takumasendeke/hygiene-hero/firmware/src/Bitmaps.cpp

#include "Bitmaps.h"

// ICON 1: Wet Hands
static const unsigned char icon[ICON_FRAMES][ICON_BYTES] PROGMEM = {
  0x00, 0x00, 0x00, 0x00, 0x00, 0x00, 0x00, 0x00, 0x00, 0x00, 0x00, 0x00,
   0x00, 0x00, 0x00, 0x00, 0x00, 0x00, 0x00, 0x00, 0x00, 0x00, 0x00, 0x00,
   0x00, 0x00, 0x00, 0x00, 0x00, 0x00, 0x00, 0x00, 0x00, 0x00, 0x00, 0x00,
   0x00, 0x00, 0x00, 0x00, 0x00, 0x00, 0x00, 0xfe, 0xff, 0xff, 0x1f, 0x00,
   0x00, 0x00, 0x00, 0x00, 0x00, 0x00, 0x00, 0x00, 0x00, 0x00, 0x00, 0xff,
   0xff, 0xff, 0xff, 0x00, 0x38, 0x8e, 0xf3, 0xef, 0x7f, 0x00, 0x00, 0x00,
   0x00, 0x00, 0x00, 0xff, 0xff, 0xff, 0xff, 0x03, 0x38, 0x8e, 0x73, 0x00,
   0x0e, 0x00, 0x00, 0x00, 0x00, 0x00, 0x00, 0x0f, 0x00, 0x00, 0xfc, 0x0f,
   0x38, 0x9f, 0x73, 0x00, 0x0e, 0x00, 0x00, 0x00, 0x00, 0x00, 0x00, 0x07,
   0x00, 0x00, 0xe0, 0x1f, 0x38, 0x9f, 0x73, 0x00, 0x0e, 0x00, 0x00, 0x00,
   0x00, 0x00, 0x00, 0x07, 0x00, 0x00, 0x80, 0x7f, 0x30, 0x9f, 0x71, 0x00,
   0x0e, 0x00, 0x00, 0x00, 0x00, 0x00, 0x00, 0x07, 0x00, 0x00, 0x00, 0xfe,
   0x70, 0xdb, 0xf1, 0x0f, 0x0e, 0x00, 0x00, 0x00, 0x00, 0x00, 0x00, 0x07,
   0x00, 0x00, 0x00, 0xfc, 0xf0, 0xfb, 0x71, 0x00, 0x0e, 0x00, 0x00, 0x00,
   0x00, 0x00, 0x00, 0x0f, 0x00, 0x00, 0x00, 0xf0, 0xf0, 0xf9, 0x70, 0x00,
   0x0e, 0x00, 0x00, 0x00, 0x00, 0x00, 0x00, 0x3f, 0x00, 0x00, 0x00, 0xe0,
   0xe0, 0xf1, 0x70, 0x00, 0x0e, 0x00, 0x00, 0x00, 0x00, 0x00, 0x00, 0xff,
   0xff, 0xff, 0x1f, 0x00, 0xe0, 0xf1, 0x70, 0x00, 0x0e, 0x00, 0x00, 0x00,
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
const uint8_t* const bitmapSteps[6][ICON_FRAMES] = {
  { icon[0],  icon[1]  },  // 0: Wet
  { icon2[0], icon2[1] },  // 1: Soap
  { icon3[0], icon3[1] },  // 2: Scrub
  { icon4[0], icon4[1] },  // 3: Rinse
  { icon5[0], icon5[1] },  // 4: Dry 
  { icon6[0], icon6[1] }   // 5: Clean
};
